formatc1702/Micro-Word-Clock/MicroWordClock2-Arduino/dutch2.h

/*
 
 VIJFTIEN
 HTWINTIG
 ALF*VOOR
 NATWAALF
 TWEENELF
 DRVIJERF
 ZNESVGEN
 ACHTTIEN
 
 // */

const int min_offset=7; // 12:00 + 5*7 min = vijfentwintig voor één

const char minutes[12][8] ={
  { // uur
    0B00000000,
    0B00000000,
    0B00000000,
    0B00000000,
    0B00000000,
    0B00000000,
    0B00000000,
    0B00000000
  }
  , { // vijf na
    0B11110000,
    0B00000000,
    0B00000000,
    0B11000000,
    0B00000000,
    0B00000000,
    0B00000000,
    0B00000000
  }
  , { // tien na
    0B00001111,
    0B00000000,
    0B00000000,
    0B11000000,
    0B00000000,
    0B00000000,
    0B00000000,
    0B00000000
  }
  ,{ // vijftien na
    0B11111111,
    0B00000000,
    0B00000000,
    0B11000000,
    0B00000000,
    0B00000000,
    0B00000000,
    0B00000000
  }
  ,{ // twintig na
    0B00000000,
    0B01111111,
    0B00000000,
    0B11000000,
    0B00000000,
    0B00000000,
    0B00000000,
    0B00000000
  }
  ,{ // vijfentwintig na
    0B11110011,
    0B01111111,
    0B00000000,
    0B11000000,
    0B00000000,
    0B00000000,
    0B00000000,
    0B00000000
  }
  ,{ // half 
    0B00000000,
    0B10000000,
    0B11100000,
    0B00000000,
    0B00000000,
    0B00000000,
    0B00000000,
    0B00000000
  }
  ,{ // vijfentwintig voor
    0B11110011,
    0B01111111,
    0B00001111,
    0B00000000,
    0B00000000,
    0B00000000,
    0B00000000,
    0B00000000
  }
  ,{ // twintig voor
    0B00000000,
    0B01111111,
    0B00001111,
    0B00000000,
    0B00000000,
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
  }
  ,{ // elf
    0B00000000,
    0B00000000,
    0B00000000,
    0B00000000,
    0B00000111,
    0B00000000,
    0B00000000,
    0B00000000
  }
};

const char blinky[8] ={
  0B00000000,
  0B00000000,
  0B00010000,
  0B00000000,
  0B00000000,
  0B00000000,
  0B00000000,
  0B00000000
};
