formatc1702/Micro-Word-Clock/MicroWordClock2-Arduino/dutch.h

/*

KTVIEJFN
WARTVOOR
OVERHALF
VIJF*EEN
TWEEAALF
ZNESVGEN
TDRVIENR
ACHTQUUR
 
 // */

const int min_offset=4; // 12:00 + 4*5 min = 10 voor half EEN

const char minutes[12][8] ={
  { // uur
    0B00000000,
    0B00000000,
    0B00000000,
    0B00000000,
    0B00000000,
    0B00000000,
    0B00000000,
    0B00000111
  }
  , { // vijf over
    0B00110110,
    0B00000000,
    0B11110000,
    0B00000000,
    0B00000000,
    0B00000000,
    0B00000000,
    0B00000000
  }
  , { // tien over
    0B01011001,
    0B00000000,
    0B11110000,
    0B00000000,
    0B00000000,
    0B00000000,
    0B00000000,
    0B00000000
  }
  ,{ // kwart over
    0B10000000,
    0B11110000,
    0B11110000,
    0B00000000,
    0B00000000,
    0B00000000,
    0B00000000,
    0B00000000
  }
  ,{ // tien voor half
    0B01011001,
    0B00001111,
    0B00001111,
    0B00000000,
    0B00000000,
    0B00000000,
    0B00000000,
    0B00000000
  }
  ,{ // vijf voor half
    0B00110110,
    0B00001111,
    0B00001111,
    0B00000000,
    0B00000000,
    0B00000000,
    0B00000000
  }
  ,{ // half
    0B00000000,
    0B00000000,
    0B00001111,
    0B00000000,
    0B00000000,
    0B00000000,
    0B00000000,
    0B00000000
  }
  ,{ // vijf over half
    0B00110110,
    0B00000000,
    0B11111111,
    0B00000000,
    0B00000000,
    0B00000000,
    0B00000000,
    0B00000000
  }
  ,{ // tien over half
    0B01011001,
    0B00000000,
    0B11111111,
    0B00000000,
    0B00000000,
    0B00000000,
    0B00000000,
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
  }
  ,{ // elf
    0B00000000,
    0B00000000,
    0B00000000,
    0B00000000,
    0B00010011,
    0B00000000,
    0B00000000,
    0B00000000
  }
};

const char blinky[8] ={
  0B00000000,
  0B00000000,
  0B00000000,
  0B00001000,
  0B00000000,
  0B00000000,
  0B00000000,
  0B00000000
};
