formatc1702/Micro-Word-Clock/MicroWordClock2-Arduino/deutsch.h

/*
 
 FÜNFZEHN
 VORNACH*
 HALBACHT
 EINSECHS
 SIEZWÖLF
 BENDREIÜ
 *ZEHNEUN
 VIER*ELF
 
 // */

const int min_offset=4; // 12:00 + 5*4 min = zehn vor halb EINS

const char minutes[12][8] ={
  { // punkt
    0B00000000,
    0B00000000,
    0B00000000,
    0B00000000,
    0B00000000,
    0B00000000,
    0B00000000,
    0B00000000
  }
  , { // fuenf nach
    0B11110000,
    0B00011110,
    0B00000000,
    0B00000000,
    0B00000000,
    0B00000000,
    0B00000000,
    0B00000000
  }
  , { // zehn nach
    0B00001111,
    0B00011110,
    0B00000000,
    0B00000000,
    0B00000000,
    0B00000000,
    0B00000000,
    0B00000000
  }
  ,{ // fuenfzehn nach
    0B11111111,
    0B00011110,
    0B00000000,
    0B00000000,
    0B00000000,
    0B00000000,
    0B00000000,
    0B00000000
  }
  ,{ // zehn vor halb
    0B00001111,
    0B11100000,
    0B11110000,
    0B00000000,
    0B00000000,
    0B00000000,
    0B00000000,
    0B00000000
  }
  ,{ // fuenf vor halb
    0B11110000,
    0B11100000,
    0B11110000,
    0B00000000,
    0B00000000,
    0B00000000,
    0B00000000
  }
  ,{ // halb
    0B00000000,
    0B00000000,
    0B11110000,
    0B00000000,
    0B00000000,
    0B00000000,
    0B00000000,
    0B00000000
  }
  ,{ // fuenf nach halb
    0B11110000,
    0B00011110,
    0B11110000,
    0B00000000,
    0B00000000,
    0B00000000,
    0B00000000,
    0B00000000
  }
  ,{ // zehn nach halb
    0B00001111,
    0B00011110,
    0B11110000,
    0B00000000,
    0B00000000,
    0B00000000,
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
  }
  ,{ // elf
    0B00000000,
    0B00000000,
    0B00000000,
    0B00000000,
    0B00000000,
    0B00000000,
    0B00000000,
    0B00000111,
  }
};

const char blinky[8] ={
  0B00000000,
  0B00000001,
  0B00000000,
  0B00000000,
  0B00000000,
  0B00000000,
  0B00000000,
  0B00000000
};
